RRAS46/Antidote_Synthesis_Forge-Puzzle/Images/ball-valve-section.png

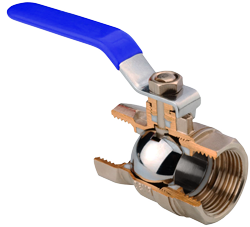
Images/ball-valve-section.png
