RRAS46/Antidote_Synthesis_Forge-Puzzle/Images/Screenshot_2.png

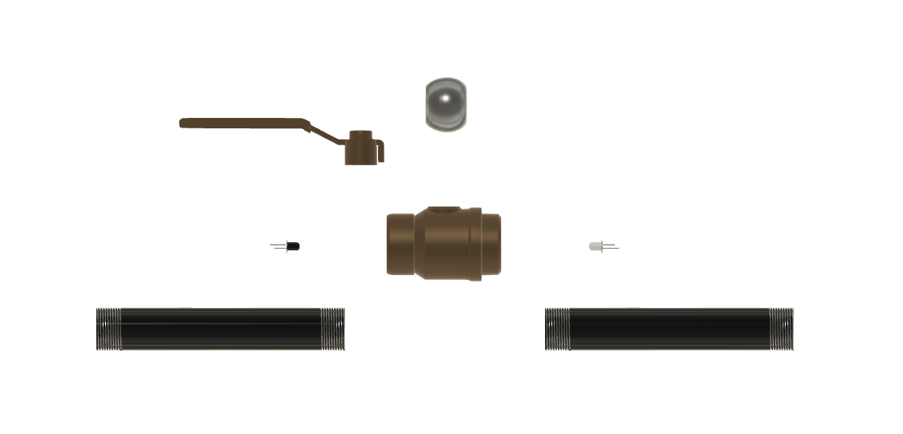
Images/Screenshot_2.png
