RRAS46/Antidote_Synthesis_Forge-Puzzle/Images/Screenshot_4.png

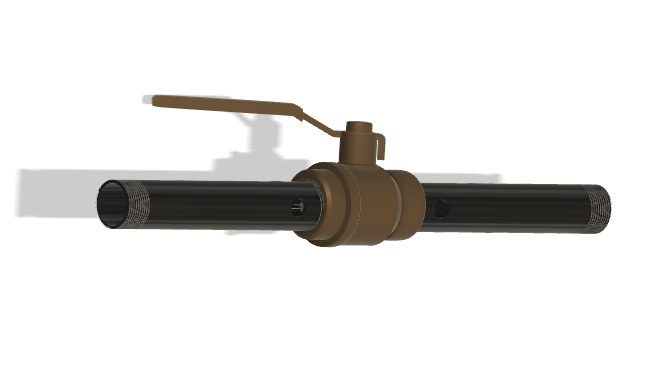
Images/Screenshot_4.png
