RRAS46/Antidote_Synthesis_Forge-Puzzle/Images/Screenshot_8.png

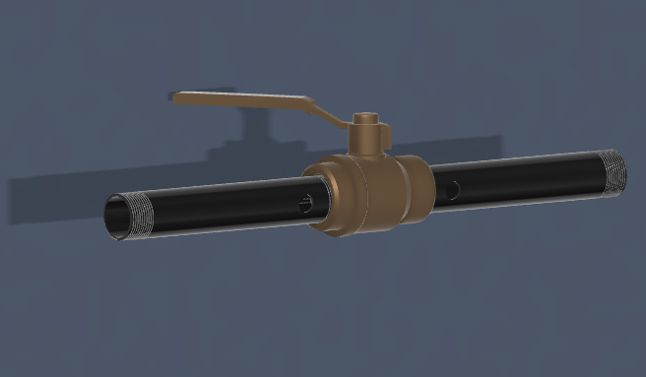
Images/Screenshot_8.png
