RRAS46/Antidote_Synthesis_Forge-Puzzle/Images/Screenshot_9.png

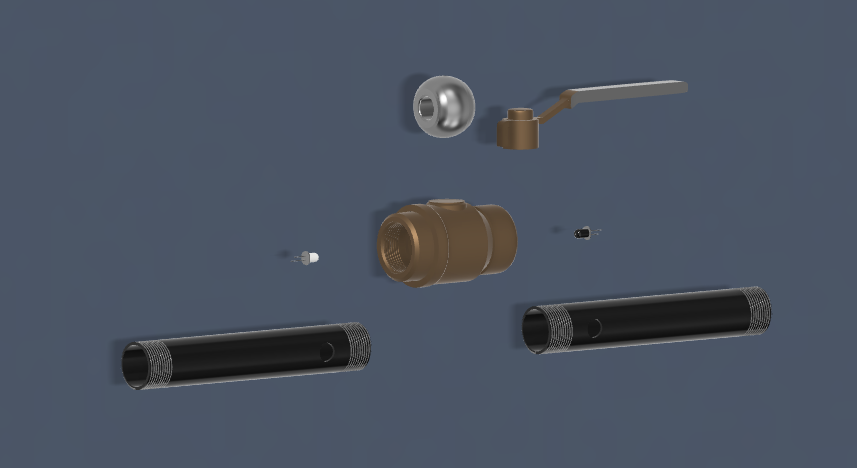
Images/Screenshot_9.png
