RRAS46/Antidote_Synthesis_Forge-Puzzle/Images/Scwsreenshot_1.png

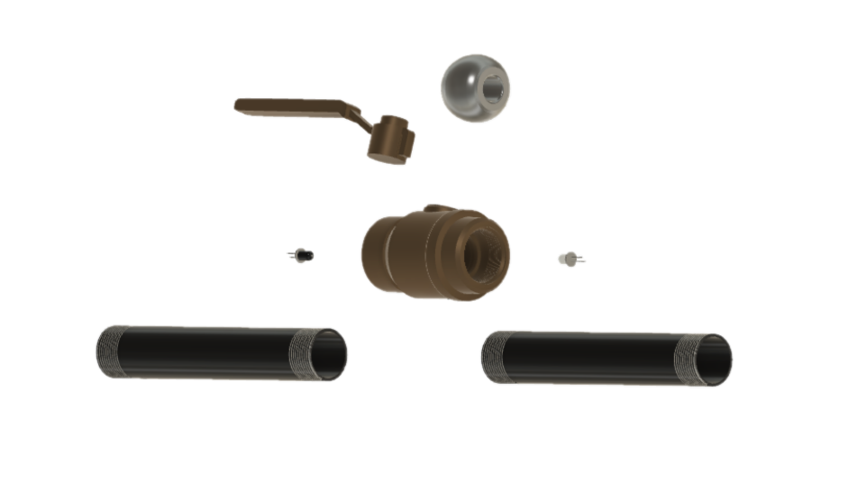
Images/Scwsreenshot_1.png
