RRAS46/Antidote_Synthesis_Forge-Puzzle/Images/UTB8XkXAgKvJXKJkSajhq6Asdsds7aFXaJ.jpg

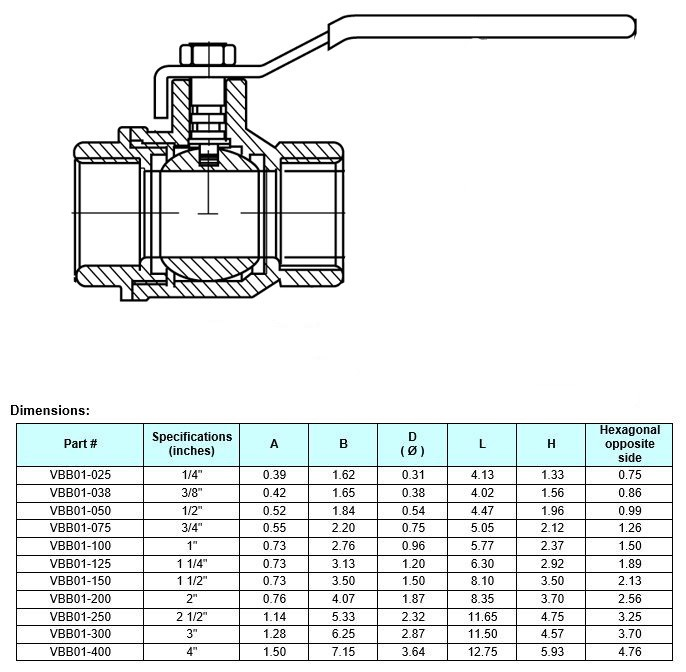
Images/UTB8XkXAgKvJXKJkSajhq6Asdsds7aFXaJ.jpg
