RRAS46/Antidote_Synthesis_Forge-Puzzle/PCB/PCB_PCB_#1-puzzle-valve_2023-10-01.png

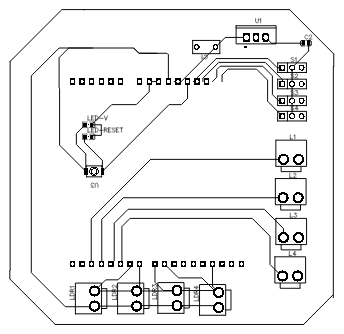
PCB/PCB_PCB_#1-puzzle-valve_2023-10-01.png
